DonovanBrenny/Handheld_Gaming_Device/firmware/Handheld-Gaming-Device.X/18x24_font_table.c

/* 
 * File:   18x24_font_table.c
 * Author: Donovan Brenny
 *
 * Created on November 20, 2025
 */


const unsigned char font_18x24[10][54] = {
    
     // ' ' (space)
    { 
      0x00, 0x00, 0x00, 0x00, 0x00, 0x00, 0x00, 0x00, 0x00, 0x00, 0x00, 0x00, 
      0x00, 0x00, 0x00, 0x00, 0x00, 0x00, 0x00, 0x00, 0x00, 0x00, 0x00, 0x00, 
      0x00, 0x00, 0x00, 0x00, 0x00, 0x00, 0x00, 0x00, 0x00, 0x00, 0x00, 0x00, 
      0x00, 0x00, 0x00, 0x00, 0x00, 0x00, 0x00, 0x00, 0x00, 0x00, 0x00, 0x00, 
      0x00, 0x00, 0x00, 0x00, 0x00, 0x00 
    },

    // 'S'
    { 
      0xF8, 0x01, 0x1C, 0xF8, 0x01, 0x1C, 0xF8, 0x01, 0x1C, 0x07, 0x0E, 0x1C, 
      0x07, 0x0E, 0x1C, 0x07, 0x0E, 0x1C, 0x07, 0x0E, 0x1C, 0x07, 0x0E, 0x1C, 
      0x07, 0x0E, 0x1C, 0x07, 0x0E, 0x1C, 0x07, 0x0E, 0x1C, 0x07, 0x0E, 0x1C, 
      0x07, 0xF0, 0x03, 0x07, 0xF0, 0x03, 0x07, 0xF0, 0x03, 0x00, 0x00, 0x00, 
      0x00, 0x00, 0x00, 0x00, 0x00, 0x00 
    },

    // 'u'
    { 
      0xC0, 0xFF, 0x03, 0xC0, 0xFF, 0x03, 0xC0, 0xFF, 0x03, 0x00, 0x00, 0x1C, 
      0x00, 0x00, 0x1C, 0x00, 0x00, 0x1C, 0x00, 0x00, 0x1C, 0x00, 0x00, 0x1C, 
      0x00, 0x00, 0x1C, 0x00, 0x80, 0x03, 0x00, 0x80, 0x03, 0x00, 0x80, 0x03, 
      0xC0, 0xFF, 0x1F, 0xC0, 0xFF, 0x1F, 0xC0, 0xFF, 0x1F, 0x00, 0x00, 0x00, 
      0x00, 0x00, 0x00, 0x00, 0x00, 0x00 
    },

    // 'p'
    { 
      0xC0, 0xFF, 0x1F, 0xC0, 0xFF, 0x1F, 0xC0, 0xFF, 0x1F, 0xC0, 0x71, 0x00, 
      0xC0, 0x71, 0x00, 0xC0, 0x71, 0x00, 0xC0, 0x71, 0x00, 0xC0, 0x71, 0x00, 
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
      0x00, 0x00, 0x00, 0x00, 0x00, 0x00, 0xFF, 0x7F, 0x1C, 0xFF, 0x7F, 0x1C, 
      0xFF, 0x7F, 0x1C, 0x00, 0x00, 0x00, 0x00, 0x00, 0x00, 0x00, 0x00, 0x00, 
      0x00, 0x00, 0x00, 0x00, 0x00, 0x00, 0x00, 0x00, 0x00, 0x00, 0x00, 0x00, 
      0x00, 0x00, 0x00, 0x00, 0x00, 0x00 
    }
};
