DonovanBrenny/Handheld_Gaming_Device/firmware/Handheld-Gaming-Device.X/6x8_font_table.c

/* 
 * File:   6x8_font_table.c
 * Author: Donovan Brenny
 *
 * Created on November 18, 2025
 */



#include "6x8_font_table.h"

const unsigned char font_6x8[96][6] = {
    
    // 32 ' ' (space)
    { 0x00, 0x00, 0x00, 0x00, 0x00, 0x00},
    
    // 33 '!'
    { 0x00, 0x00, 0x5F, 0x00, 0x00, 0x00},
    
    // 34 '"'
    { 0x00, 0x07, 0x00, 0x07, 0x00, 0x00},
    
    // 35 '#'
    { 0x14, 0x7F, 0x14, 0x7F, 0x14, 0x00},
    
    // 36 '$'
    { 0x24, 0x2A, 0x7F, 0x2A, 0x12, 0x00},
    
    // 37 '%'
    { 0x23, 0x13, 0x08, 0x64, 0x62, 0x00},
    
    // 38 '&'
    { 0x36, 0x49, 0x55, 0x22, 0x50, 0x00},
    
    // 39 '''
    { 0x00, 0x05, 0x03, 0x00, 0x00, 0x00},
    
    // 40 '('
    { 0x00, 0x1C, 0x22, 0x41, 0x00, 0x00},
    
    // 41 ')'
    { 0x00, 0x41, 0x22, 0x1C, 0x00, 0x00},
    
    // 42 '*'
    { 0x14, 0x08, 0x3E, 0x08, 0x14, 0x00},
    
    // 43 '+'
    { 0x08, 0x08, 0x3E, 0x08, 0x08, 0x00},
    
    // 44 ','
    { 0x00, 0x50, 0x30, 0x00, 0x00, 0x00},
    
    // 45 '-'
    { 0x08, 0x08, 0x08, 0x08, 0x08, 0x00},
    
    // 46 '.'
    { 0x00, 0x60, 0x60, 0x00, 0x00, 0x00},
    
    // 47 '/'
    { 0x20, 0x10, 0x08, 0x04, 0x02, 0x00},
    
    // 48 '0'
    { 0x3E, 0x51, 0x49, 0x45, 0x3E, 0x00},
    
    // 49 '1'
    { 0x00, 0x42, 0x7F, 0x40, 0x00, 0x00},
    
    // 50 '2'
    { 0x42, 0x61, 0x51, 0x49, 0x46, 0x00},
    
    // 51 '3'
    { 0x21, 0x41, 0x45, 0x4B, 0x31, 0x00},
    
    // 52 '4'
    { 0x18, 0x14, 0x12, 0x7F, 0x10, 0x00},
    
    // 53 '5'
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

    // 122 'z'
    { 0x44, 0x64, 0x54, 0x4C, 0x44, 0x00},

    // 123 '{'
    { 0x00, 0x08, 0x36, 0x41, 0x00, 0x00},

    // 124 '|'
    { 0x00, 0x00, 0x7F, 0x00, 0x00, 0x00},

    // 125 '}'
    { 0x00, 0x41, 0x36, 0x08, 0x00, 0x00},

    // 126 '~'
    { 0x08, 0x04, 0x08, 0x10, 0x08, 0x00}
};
