DonovanBrenny/Handheld_Gaming_Device/firmware/Handheld-Gaming-Device.X/18x24_font_table.h

/* 
 * File:   18x24_font_table.h
 * Author: dbren
 *
 * Created on November 20, 2025, 4:51 PM
 */

#ifndef 18X24_FONT_TABLE_H
#define	18X24_FONT_TABLE_H

#ifdef	__cplusplus
extern "C" {
#endif

    #define FONT_6x8_WIDTH 6
    #define FONT_6x8_HEIGHT 8
    
    extern const unsigned char font_6x8[96][6];


#ifdef	__cplusplus
}
#endif

#endif	/* 18X24_FONT_TABLE_H */
